JunjiangGuo/2023_2024_mini_project_Junjiang_Thang_Stephane/Piste_Blue/Chirpstack/Chirpstack_application_configuration.png

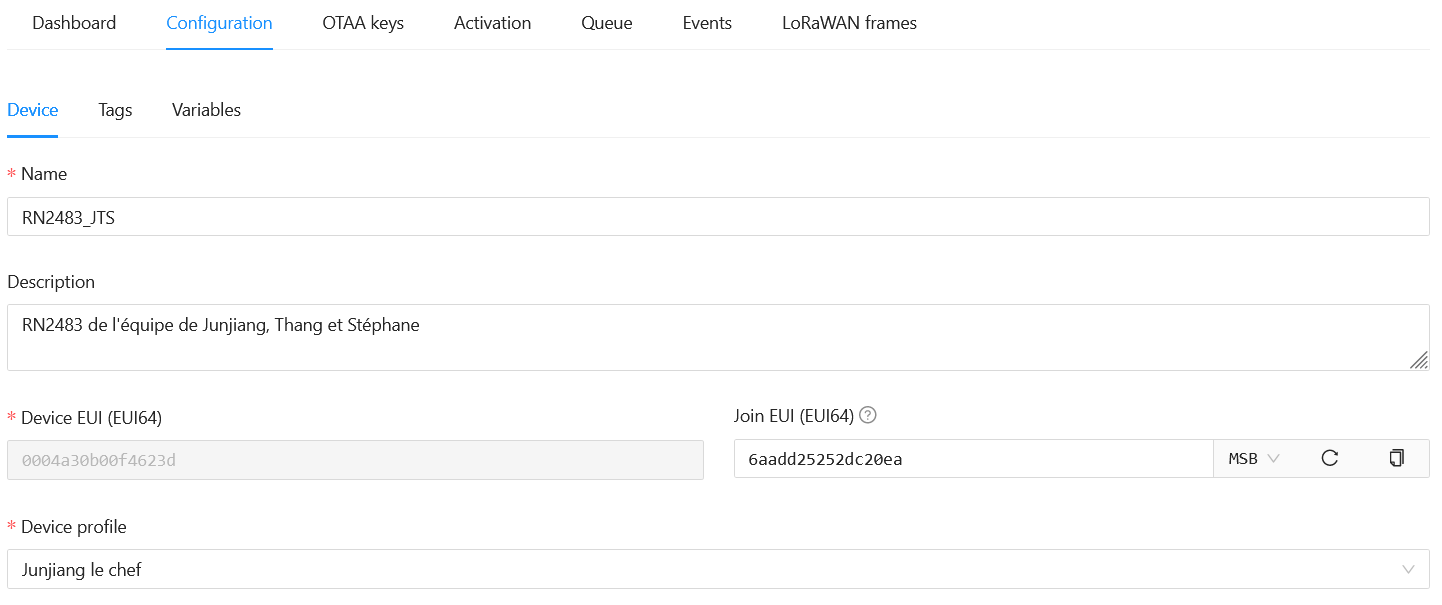
Piste_Blue/Chirpstack/Chirpstack_application_configuration.png
